taupau/maize-made-arcade/game/common/bg.png

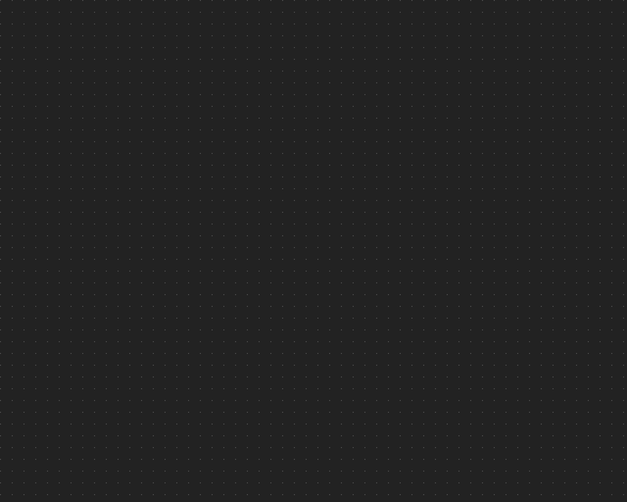
game/common/bg.png
