taupau/maize-made-arcade/game/common/image.png

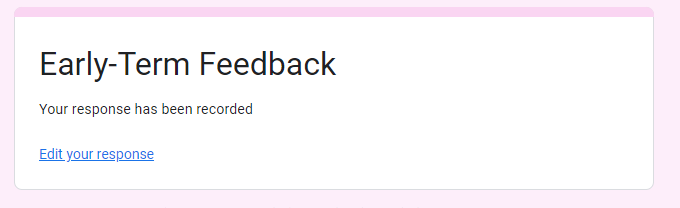
game/common/image.png
