taupau/maize-made-arcade/game/.godot/editor/editor_layout.cfg

[docks]

dock_filesystem_split=0
dock_filesystem_display_mode=0
dock_filesystem_file_sort=0
dock_filesystem_file_list_display_mode=1
dock_split_2=0
dock_split_3=0
dock_hsplit_1=0
dock_hsplit_2=464
dock_hsplit_3=-270
dock_hsplit_4=0
dock_1_selected_tab_idx=0
dock_2_selected_tab_idx=0
dock_3_selected_tab_idx=0
dock_4_selected_tab_idx=0
dock_5_selected_tab_idx=0
dock_6_selected_tab_idx=0
dock_7_selected_tab_idx=0
dock_8_selected_tab_idx=0
dock_floating={}
dock_filesystem_selected_paths=PackedStringArray("res://")
dock_filesystem_uncollapsed_paths=PackedStringArray("res://")
dock_3="Scene,Import"
dock_4="FileSystem"
dock_5="Inspector,Node,History"

[EditorNode]

open_scenes=PackedStringArray("res://games/pong/pong.tscn", "res://games/pong/menu.tscn", "res://games/pong/game_over.tscn", "res://main.tscn", "res://games/asteroids/asteroids.tscn")
current_scene="res://games/asteroids/asteroids.tscn"
center_split_offset=0
selected_default_debugger_tab_idx=0
selected_main_editor_idx=0

[ScriptEditor]

open_scripts=["res://games/asteroids/asteroids.gd"]
open_help=[]
script_split_offset=150
list_split_offset=0
selected_script="res://games/asteroids/asteroids.gd"

[ShaderEditor]

open_shaders=[]
split_offset=0
selected_shader=""
